paritkary25/SysMon/USB-C_dim_xtracn/detected_circles.jpg

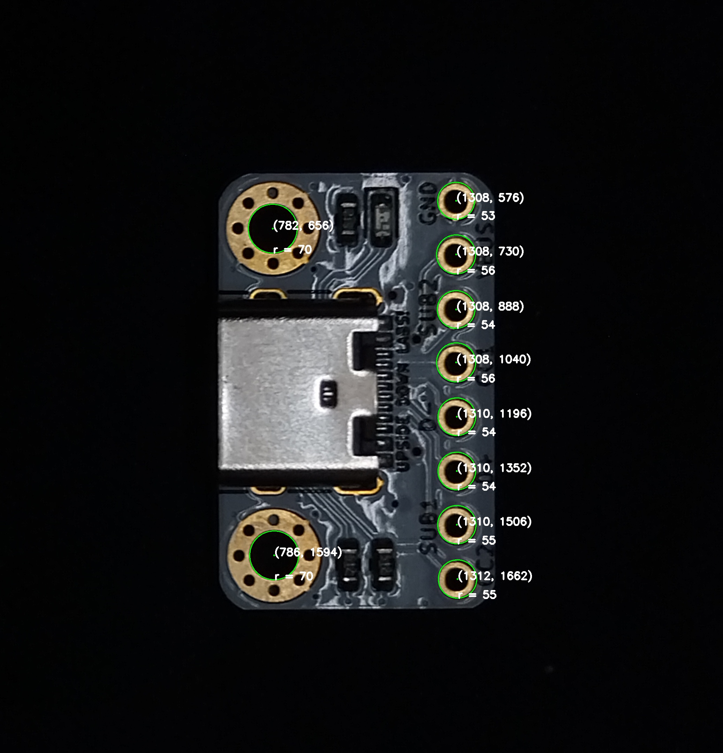
USB-C_dim_xtracn/detected_circles.jpg
