paritkary25/SysMon/CAD/gateron_sw.FCStd

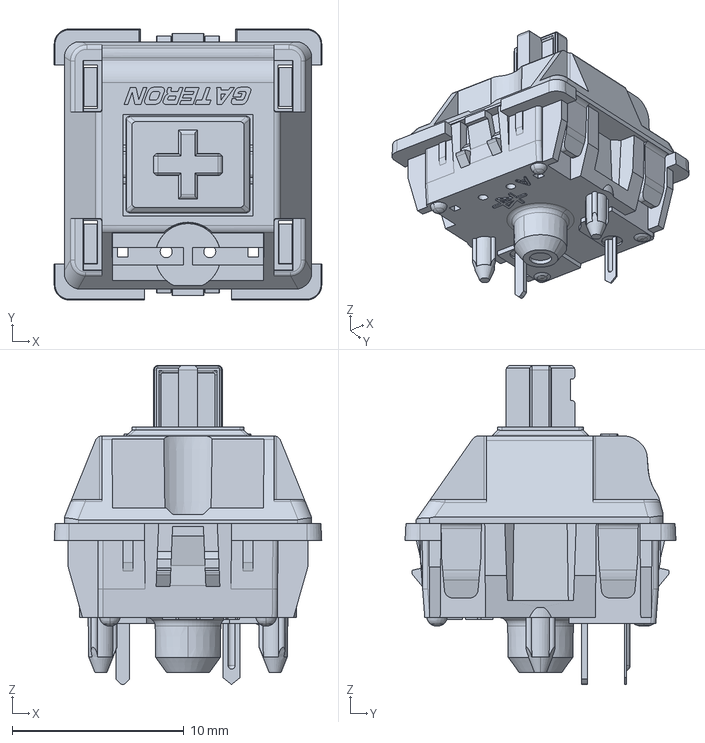
[picture p15: CAD file, 2026-01-02]
CAD/gateron_sw.FCStd
15.6 x 15.8 x 18.6 mm
