paritkary25/SysMon/CAD/UBA-4R-D14T-4D.FCStd

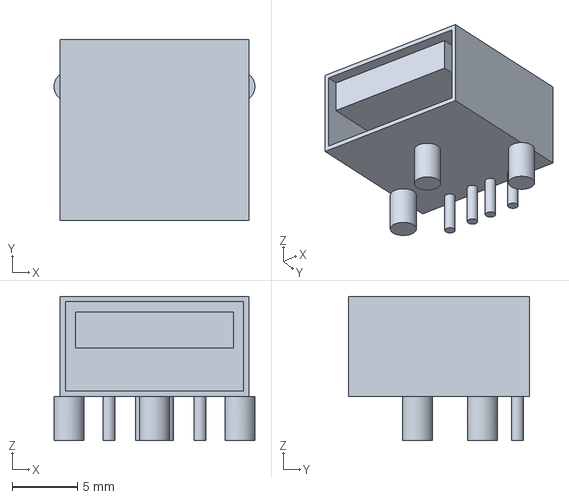
[picture p16: CAD file, 2026-01-02]
CAD/UBA-4R-D14T-4D.FCStd
15.4 x 13.9 x 11.1 mm
