paritkary25/SysMon/CAD/SysMon_CAD-LidBody.step

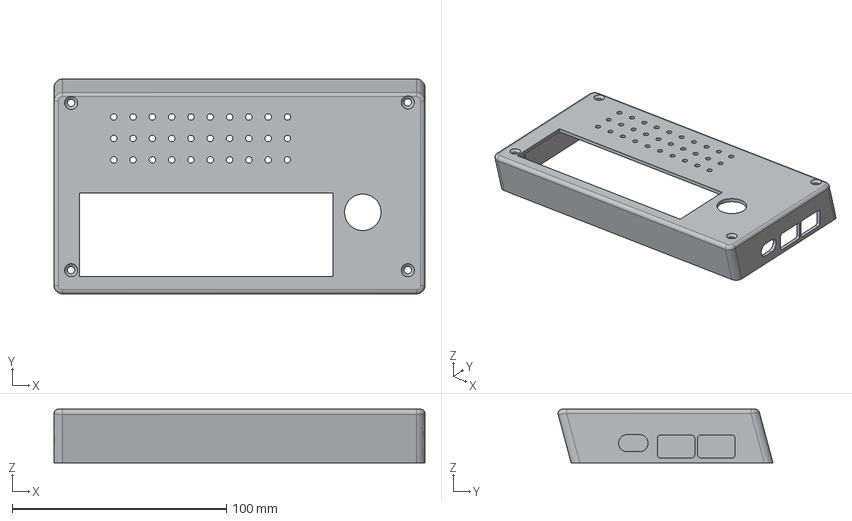
[picture p17: CAD file, 2026-01-02]
CAD/SysMon_CAD-LidBody.step
173.0 x 100.2 x 25.0 mm
