paritkary25/SysMon/CAD/EC11.FCStd

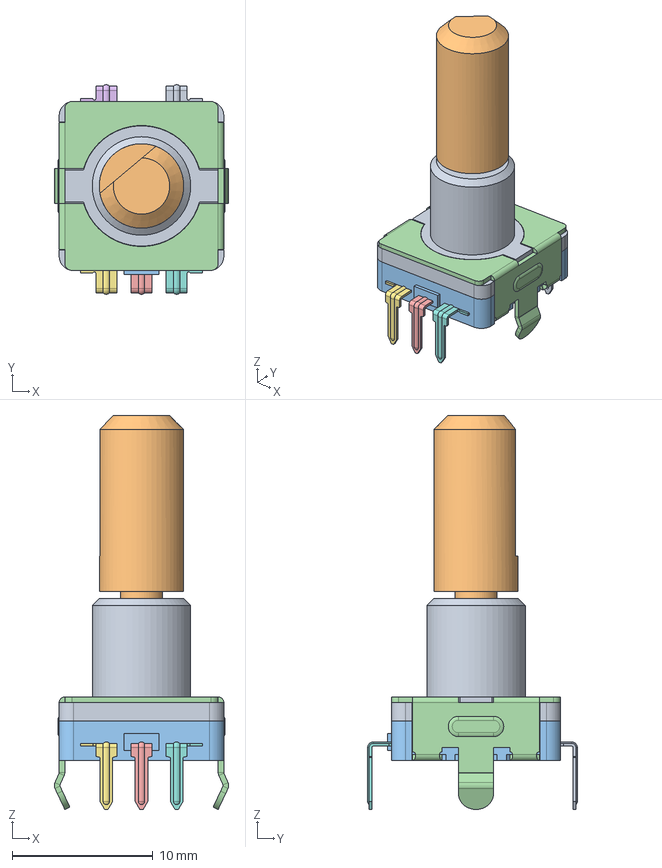
[picture p18: CAD file, 2026-01-02]
CAD/EC11.FCStd
12.4 x 14.9 x 28.0 mm
EC11-Base
EC11-Shaft-F
EC11-Housing-THT
EC11-Housing-THT001
EC11-Housing-THT002
EC11-Housing-THT003
EC11-Housing-THT004
EC11-Housing-THT005
EC11-Housing-THT006
